cbosoft/pi_rheo_proj/etc/gd_demon.png

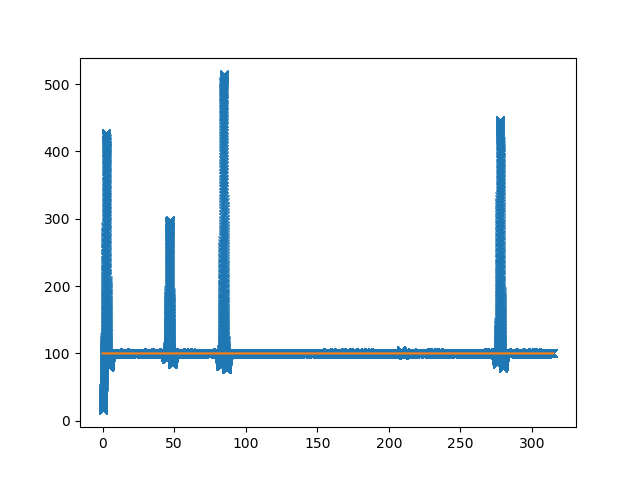
etc/gd_demon.png
