cbosoft/pi_rheo_proj/plots/logs_piezo_compare_antiderivatives.png

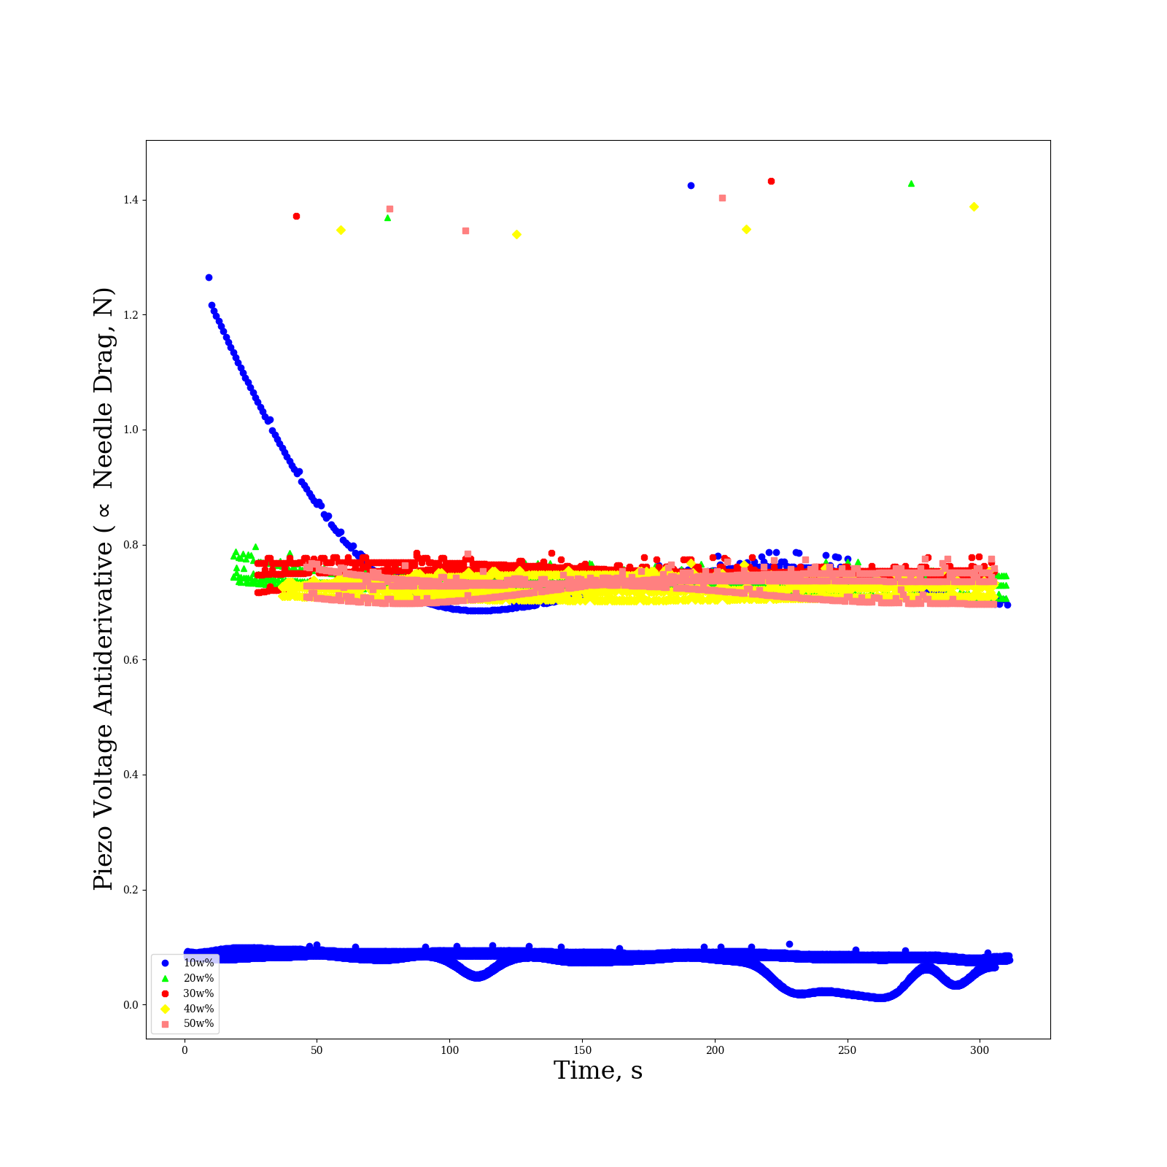
plots/logs_piezo_compare_antiderivatives.png
