cbosoft/pi_rheo_proj/plots/logs_tau_v_gd.png

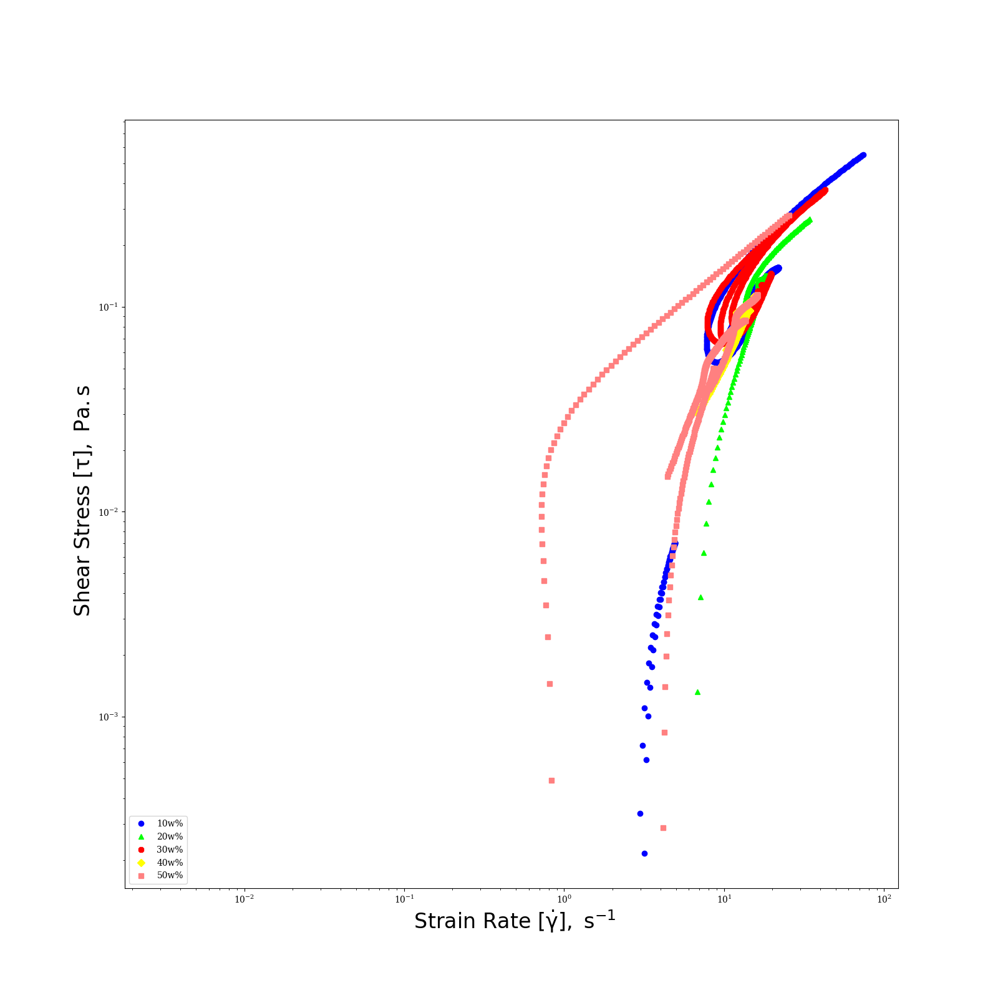
plots/logs_tau_v_gd.png
