cbosoft/pi_rheo_proj/logs/rheometry_test_filter_test_8_290817_1105.csv

t | dr | fdr | cra | crb | pv | T | Vpz
1504004722.269784 | 0.203 | 0.151 | 1.550 | 1.534 | 62 | 17.000 | 0.78955078125
1504004723.194897 | 0.203 | 0.151 | 1.502 | 1.492 | 62 | 17.000 | 0.77021484375
1504004724.114897 | 0.184 | 0.148 | 1.492 | 1.492 | 62 | 17.000 | 0.80244140625
1504004725.034899 | 0.142 | 0.135 | 1.492 | 1.502 | 62 | 17.000 | 0.7798828125
1504004725.954882 | 0.119 | 0.132 | 1.518 | 1.534 | 62 | 17.062 | 0.80244140625
1504004727.694893 | 0.068 | 0.106 | 1.492 | 1.502 | 62 | 17.000 | 0.80244140625
1504004728.614887 | 0.168 | 0.119 | 1.560 | 1.560 | 62 | 17.062 | 0.7798828125
1504004729.534799 | 0.184 | 0.119 | 1.560 | 1.502 | 62 | 17.062 | 0.7798828125
1504004730.454874 | 0.142 | 0.132 | 1.544 | 1.550 | 62 | 17.062 | 0.812109375
1504004731.374855 | 0.203 | 0.119 | 1.560 | 1.563 | 62 | 17.062 | 0.7798828125
1504004732.294886 | 0.132 | 0.119 | 1.511 | 1.511 | 62 | 17.062 | 0.7798828125
1504004733.214926 | 0.148 | 0.116 | 1.502 | 1.502 | 62 | 17.062 | 0.7798828125
1504004734.134880 | 0.135 | 0.151 | 1.511 | 1.518 | 62 | 17.062 | 0.7798828125
1504004735.054887 | 0.193 | 0.129 | 1.518 | 1.511 | 62 | 17.062 | 0.78955078125
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
