cbosoft/pi_rheo_proj/logs/rheometry_test_glyc_0_081117_1416.csv

t | spd0 | spd1 | spd2 | spd3 | spd4 | spd5 | Vcr | adc0 | dc | T | Vpz | Vms
1510150604.269030 | 0.000 | 0.000 | 3.140 | 3.140 | 3.140 | 3.140 | 2.558 | 0.003 | 19.566 | 13.562 | 0.125806451613 | 0.284
1510150604.339099 | 0.000 | 0.000 | 3.140 | 3.140 | 3.140 | 3.140 | 2.571 | 0.048 | 19.934 | 13.562 | 0.109677419355 | 0.310
1510150604.351540 | 0.000 | 0.000 | 3.140 | 3.140 | 3.140 | 3.140 | 2.574 | 0.000 | 20.250 | 13.562 | 0.0 | 0.323
1510150604.363374 | 0.000 | 0.000 | 3.140 | 3.140 | 3.140 | 3.140 | 2.600 | 0.042 | 20.560 | 13.562 | 0.132258064516 | 0.335
1510150604.374815 | 0.000 | 0.000 | 3.140 | 3.140 | 3.140 | 3.140 | 2.584 | 0.000 | 20.867 | 13.562 | 0.0 | 0.348
1510150604.386167 | 0.000 | 0.000 | 3.140 | 3.140 | 3.140 | 3.140 | 2.626 | 0.016 | 21.169 | 13.562 | 0.0451612903226 | 0.361
1510150604.397441 | 0.000 | 0.000 | 3.140 | 3.140 | 3.140 | 3.140 | 2.574 | 0.010 | 21.467 | 13.562 | 0.0677419354839 | 0.374
1510150604.408643 | 0.000 | 0.000 | 3.140 | 3.140 | 3.140 | 3.140 | 2.597 | 0.000 | 21.764 | 13.562 | 0.0 | 0.387
1510150604.419846 | 0.000 | 0.000 | 3.140 | 3.140 | 3.140 | 3.140 | 2.590 | 0.039 | 22.062 | 13.562 | 0.11935483871 | 0.400
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
