cbosoft/pi_rheo_proj/logs/rheometry_test_mostlyglycerol_091017_1301.csv

t | f_spd0 | r_spd0 | f_spd1 | r_spd1 | f_spd2 | r_spd2 | cra | crb | T | Vpz | Vms | gamma_dot | tau | mu_en_bal | mu_current_relation
1507554089.4 | 0.0 | 0.0 | 0.0 | 0.0 | 0.0 | 0.0 | 2.548 | 0.368 | -3.18227000293e-05 | 0.0258064516129 | 0.873599662306 | 196.45501172 | -683.603416061 | 1.52997200709e-05 | -3.47969446071
1507554089.42 | 0.0 | 0.0 | 0.0 | 0.0 | 0.0 | 0.0 | 2.519 | 0.165 | -3.08365434459e-05 | 0.0161290322581 | 0.891087154863 | 210.641052324 | -662.419166813 | 1.363333654e-05 | -3.14477714341
1507554089.43 | 0.0 | 0.0 | 0.0 | 0.0 | 0.0 | 0.0 | 2.555 | 0.071 | -2.98462907404e-05 | 0.0 | 0.908736202035 | 225.204923712 | -641.14692619 | 1.22158959829e-05 | -2.84694897261
1507554089.45 | 0.0 | 0.0 | 0.0 | 0.0 | 0.0 | 0.0 | 2.529 | 0.042 | -2.88517608802e-05 | 0.041935483871 | 0.926541915813 | 240.150931388 | -619.782805321 | 1.10006754069e-05 | -2.58080533663
1507554089.46 | 0.0 | 0.0 | 0.0 | 0.0 | 0.0 | 0.0 | 2.542 | 0.019 | -2.78527884582e-05 | 0.0 | 0.944499224461 | 255.483290905 | -598.323250991 | 9.95137534663e-06 | -2.34192713297
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
