cbosoft/pi_rheo_proj/logs/rheometry_test_mostlyglycerol_091017_1301_calcd.csv

t | f_spd0 | r_spd0 | f_spd1 | r_spd1 | f_spd2 | r_spd2 | cra | crb | T | Vpz | Vms | gamma_dot | tau | mu_en_bal | mu_current_relation
1507554089.4 | 0.0 | 0.0 | 0.0 | 0.0 | 0.0 | 0.0 | 2.548 | 0.368 | -3.18227000293e-05 | 0.0258064516129 | 0.873599662306 | 294.681579451 | -3.18227000293e-05 | 6.79991888241e-06 | -1.07990123063e-07
1507554089.42 | 0.0 | 0.0 | 0.0 | 0.0 | 0.0 | 0.0 | 2.519 | 0.165 | -3.08365434459e-05 | 0.0161290322581 | 0.891087154863 | 315.960594709 | -3.0836543446e-05 | 6.05929841682e-06 | -9.75961685169e-08
1507554089.43 | 0.0 | 0.0 | 0.0 | 0.0 | 0.0 | 0.0 | 2.555 | 0.071 | -2.98462907404e-05 | 0.0 | 0.908736202035 | 337.806355124 | -2.98462907403e-05 | 5.42932022653e-06 | -8.8353254128e-08
1507554089.45 | 0.0 | 0.0 | 0.0 | 0.0 | 0.0 | 0.0 | 2.529 | 0.042 | -2.88517608802e-05 | 0.041935483871 | 0.926541915813 | 360.225318944 | -2.88517608802e-05 | 4.88921833598e-06 | -8.00936507316e-08
1507554089.46 | 0.0 | 0.0 | 0.0 | 0.0 | 0.0 | 0.0 | 2.542 | 0.019 | -2.78527884582e-05 | 0.0 | 0.944499224461 | 383.223809495 | -2.78527884582e-05 | 4.42285949795e-06 | -7.26802139327e-08
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
