cbosoft/pi_rheo_proj/etc/pmt.py

from sys import path
path.append("./../bin/")

import motor
import resx
from time import sleep
m= motor.motor()
m.start_poll(name="test.csv", controlled=False)
m.pidc.tuning = [0.75, 3.0, 0.0]
m.update_setpoint(150)
m.set_dc(25)
print "wait"
for i in range(0, 90):
    print "speed  {:.3f}  gd {:.3f}  lav  {} err {}  T {}".format(m.speed, resx.get_strain((m.speed * 2 * 3.14) / 60.0), m.ldc, m.pidc.lerr, m.temperature_c)
    sleep(1)
#m.start_control()
#print "controlling"
#for i in range(0, 60):
#    print "speed  {:.3f}  gd {:.3f}  lav  {} err {}".format(m.speed, resx.get_strain((m.speed * 2 * 3.14) / 60.0), m.ldc, m.pidc.lerr)
#    sleep(1)
m.clean_exit()
